Pike1950/fmcw-radar-portfolio/docs/planning/PCB_Layout_Change_Plan.docx

# FMCW Radar Baseband Rev B

PCB Layout Change Plan

Bradley Ward - March 2026

# Progress Summary

Status | Count | Items | Priority
PENDING | 3 of 8 | PCB-01 through PCB-03 | [P0] Critical
PENDING | 3 of 8 | PCB-04 through PCB-06 | [P1] Important
PENDING | 2 of 8 | PCB-07, PCB-08 | [P2] Final

# Overview

This document itemizes every task required to take the Rev B baseband from a frozen schematic to a manufactured PCB. Tasks are organized by priority and follow the natural layout workflow: stackup definition, component placement, ground strategy, signal routing, power routing, DFT placement, and final validation.

Prerequisites: Schematic must be frozen (SCH-09 complete) with 0 ERC errors before PCB layout begins.

Target: 4-layer PCB (OSHPark), single continuous ground plane, partitioned analog/digital routing, all bypass caps within placement distance spec, DRC-clean, ready for manufacturing.

# Change Summary

ID | Pri | Status | Task | File(s)
PCB-01 | [P0] | [PENDING] | Define 4-layer stackup | KiCad Board Setup
PCB-02 | [P0] | [PENDING] | Component placement - analog signal path | KiCad PCB Editor
PCB-03 | [P0] | [PENDING] | Ground plane strategy - single plane, partitioned routing | KiCad PCB Editor (L2 copper zone)
PCB-04 | [P1] | [PENDING] | Critical trace routing - analog signal path | KiCad PCB Editor
PCB-05 | [P1] | [PENDING] | Power distribution routing | KiCad PCB Editor (L3 and L1 power traces
PCB-06 | [P1] | [PENDING] | DFT connector and test point placement | KiCad PCB Editor
PCB-07 | [P2] | [PENDING] | Design rule check and manufacturing review | KiCad DRC
PCB-08 | [P2] | [PENDING] | Silkscreen and documentation | KiCad PCB Editor (F.Silkscreen, B.Silksc

# Detailed Task Descriptions

## PCB-01: Define 4-layer stackup [PENDING]

Priority | [P0]
Status | PENDING
File(s) | KiCad Board Setup
Risk | Low - standard 4-layer stackup. Must be decided before any routing.

What

The PCB uses a 4-layer stackup. Layer assignment must be defined before placement or routing begins.

Action

Configure KiCad board setup with: L1 (F.Cu) = Signal + Components, L2 (In1.Cu) = Ground plane (continuous, unbroken), L3 (In2.Cu) = Power plane (3V3A, 3V3D zones), L4 (B.Cu) = Signal + Components. Set design rules: trace width 0.2mm (signal), 0.3mm (power), clearance 0.15mm, via drill 0.3mm.

Why

A continuous ground plane on L2 provides the lowest-impedance return current path for all signals. Power on L3 keeps power routing off the signal layers. This is the standard mixed-signal 4-layer stackup recommended by TI, Analog Devices, and Eric Bogatin.

Implementation Notes

OSHPark 4-layer service uses a fixed stackup: 6.7 mil / 47 mil / 6.7 mil dielectric. Impedance approximately 50 ohm for 8 mil trace over the L2 ground plane.

## PCB-02: Component placement - analog signal path [PENDING]

Priority | [P0]
Status | PENDING
File(s) | KiCad PCB Editor
Risk | Medium - placement determines routing quality and noise coupling.

What

Place all components following the signal flow: J_IF (SMA) at board edge, Sheet B components in a line, PGA113 centrally, filter passives near LTC6242, FDA and ADC close together, J_DFT at opposite board edge.

Action

Place in signal-flow order: J_IF (edge) -> R_IN -> D_ESD -> C_AC -> R_BIAS -> PGA113 -> R_FILT_ISO -> R3/R4/C13/C14 -> LTC6242 -> R5/R6/C15/C16 -> FDA (THS4531A) -> R_OUTP/R_OUTM/C_DIFF -> ADS8881 -> J_DFT (edge). Bypass caps within 2mm of their IC pins. Power components (LDO, ferrite, references) grouped separately from signal path.

Why

Component placement that follows signal flow minimizes trace length, reduces parasitic inductance and capacitance, and keeps the analog signal path compact. Bypass cap placement distance derived from trace impedance analysis (System Design Document Section 3.1.3).

Implementation Notes

DFT components (test points, MMCX connectors) should be accessible from the board edge. MMCX connectors are DNP (Do Not Populate) by default.

## PCB-03: Ground plane strategy - single plane, partitioned routing [PENDING]

Priority | [P0]
Status | PENDING
File(s) | KiCad PCB Editor (L2 copper zone)
Risk | Medium - incorrect ground strategy is the #1 cause of mixed-signal noise issues.

What

Use a single, continuous ground plane on L2 with no splits or cuts. Route analog and digital signals on different areas of the board but share the same ground plane.

Action

Pour a continuous GND copper zone on L2 covering the entire board. Do NOT split the ground plane between analog and digital. Instead, partition the signal routing: analog signals on one side, digital (SPI, CONVST) on the other. The ferrite bead (FB1) separates 3V3A from 3V3D on the power plane (L3), not the ground plane.

Why

A split ground plane forces return currents to find alternative paths, often crossing the split and creating ground loops. A single continuous ground provides the lowest-impedance return path for all signals. The analog/digital separation happens at the power level (ferrite bead) and routing level (partitioned traces), not the ground level. This is the approach recommended by Henry Ott and Bruce Archambeault.

Implementation Notes

GNDD is used only for C4 and C5 (3V3D side decoupling). These connect to the main GND plane through a single via near the ferrite bead.

## PCB-04: Critical trace routing - analog signal path [PENDING]

Priority | [P1]
Status | PENDING
File(s) | KiCad PCB Editor
Risk | Medium - signal integrity depends on trace routing quality.

What

Route the analog signal path traces with attention to length, width, spacing from digital traces, and return current path continuity.

Action

Route analog signal traces on L1 (F.Cu) over the continuous L2 ground plane. Keep analog traces away from SPI/digital traces (minimum 2mm separation or use ground guard traces). Route bypass cap connections as short as possible (target: less than 2mm for 100nF caps per Section 3.1.3 analysis). Route the FDA differential outputs (OUTP/OUTM) as a matched pair with equal length and spacing.

Why

The analog signal path carries microvolt-level signals (at high PGA gain). Any noise coupling from digital switching (SPI clock at up to 10 MHz) will degrade the SNR. The ground plane provides a low-impedance return path, but only if the signal traces run directly over it without crossing voids or splits.

Implementation Notes

The FDA differential pair (OUTP/OUTM) is the most critical routing. Length mismatch between the two traces creates timing skew that degrades the ADC's differential measurement.

## PCB-05: Power distribution routing [PENDING]

Priority | [P1]
Status | PENDING
File(s) | KiCad PCB Editor (L3 and L1 power traces)
Risk | Low - power routing is less sensitive than signal routing.

What

Route power distribution on L3 (power plane) with copper pours for 3V3A and 3V3D zones, separated by the ferrite bead footprint.

Action

Create two copper zones on L3: 3V3A (covering the analog section) and 3V3D (covering only the J_DFT/digital area). The ferrite bead (FB1) bridges the two zones. 5V input trace from ST1 to LDO on L1 or L3, with adequate width (0.5mm minimum for 200mA). Place decoupling cap vias close to IC power pins with short connections to L3 power zone and L2 ground plane.

Why

Keeping power distribution on a dedicated layer avoids interference with signal routing and provides low-impedance power delivery. The ferrite bead physically separates the analog and digital power zones, which is the primary mechanism for analog/digital isolation in this design.

Implementation Notes

The 3V3D zone is intentionally small - it only powers J_DFT VCC and pull-up resistors. All IC power pins connect to 3V3A.

## PCB-06: DFT connector and test point placement [PENDING]

Priority | [P1]
Status | PENDING
File(s) | KiCad PCB Editor
Risk | Low - DFT placement is flexible.

What

Place J_DFT, test points, and MMCX connectors for board-edge accessibility.

Action

J_DFT (2x10 header) at one board edge, oriented for ribbon cable connection. Test points (TP_5V, TP_3V3A, TP_VREF, TP_VCM, TP_GND, TP_IF_RAW, TP_PGA_IN, TP_PGA_OUT, TP_LPF_OUT, TP_AINP, TP_AINN, TP_FDA_OUTP, TP_FDA_OUTN) accessible with a scope probe. MMCX connectors (J_MMCX_PGA, J_MMCX_LPF, plus 3 on Sheet D) near their signal points but at board edge.

Why

DFT-first design methodology requires that every critical signal be measurable without invasive probing. Test points and MMCX connectors enable bringup validation, filter characterization (Bode plot via MMCX), and fault isolation.

Implementation Notes

MMCX connectors are DNP by default. They are placed on the PCB with footprints but not soldered unless needed for characterization.

## PCB-07: Design rule check and manufacturing review [PENDING]

Priority | [P2]
Status | PENDING
File(s) | KiCad DRC
Risk | Low - final validation step.

What

Run KiCad DRC to verify all design rules are met. Review Gerber outputs against OSHPark specifications.

Action

Run DRC with target: 0 errors, 0 warnings. Verify: minimum trace width (0.15mm), minimum clearance (0.15mm), minimum via drill (0.3mm), minimum annular ring. Export Gerbers and drill files. Verify against OSHPark 4-layer specifications.

Why

DRC is the gate for manufacturing. Any violations must be resolved before ordering boards.

Implementation Notes

OSHPark 4-layer: 0.8mm board thickness, ENIG finish, purple soldermask. Minimum order: 3 boards.

## PCB-08: Silkscreen and documentation [PENDING]

Priority | [P2]
Status | PENDING
File(s) | KiCad PCB Editor (F.Silkscreen, B.Silkscreen)
Risk | None - cosmetic only.

What

Add reference designators, polarity marks, pin 1 indicators, test point labels, and project identification to the silkscreen.

Action

Label all components with reference designators (visible, readable at 0.8mm text height minimum). Add polarity marks for D1 (BAT54S), D_ESD. Mark Pin 1 on all ICs. Label test points with signal names. Add project title, revision, and date to silkscreen.

Why

Clear silkscreen labeling is essential for assembly and debug. A technician should be able to identify any component and its orientation from the silkscreen alone.

Implementation Notes

Include 'Rev B' and date on the board. Consider adding the signal flow diagram or block labels near component groups.
